shufps/peak-ignitor-hw/case/case.png

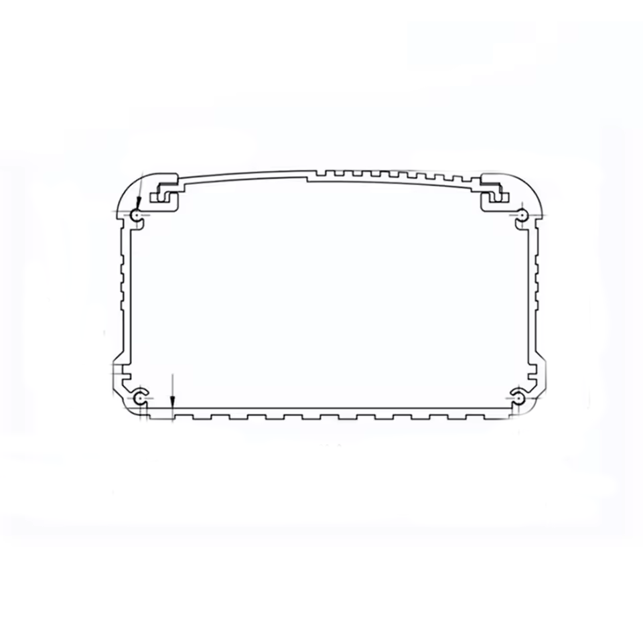
case/case.png
