shufps/peak-ignitor-hw/images/front.jpg

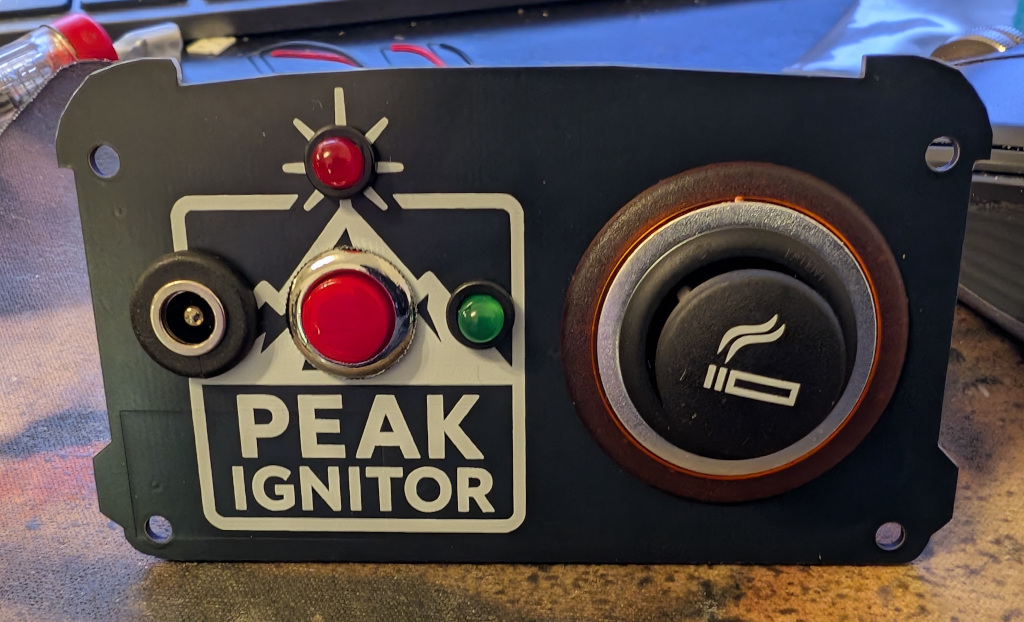
images/front.jpg
