shufps/peak-ignitor-hw/images/heatsink-front.jpg

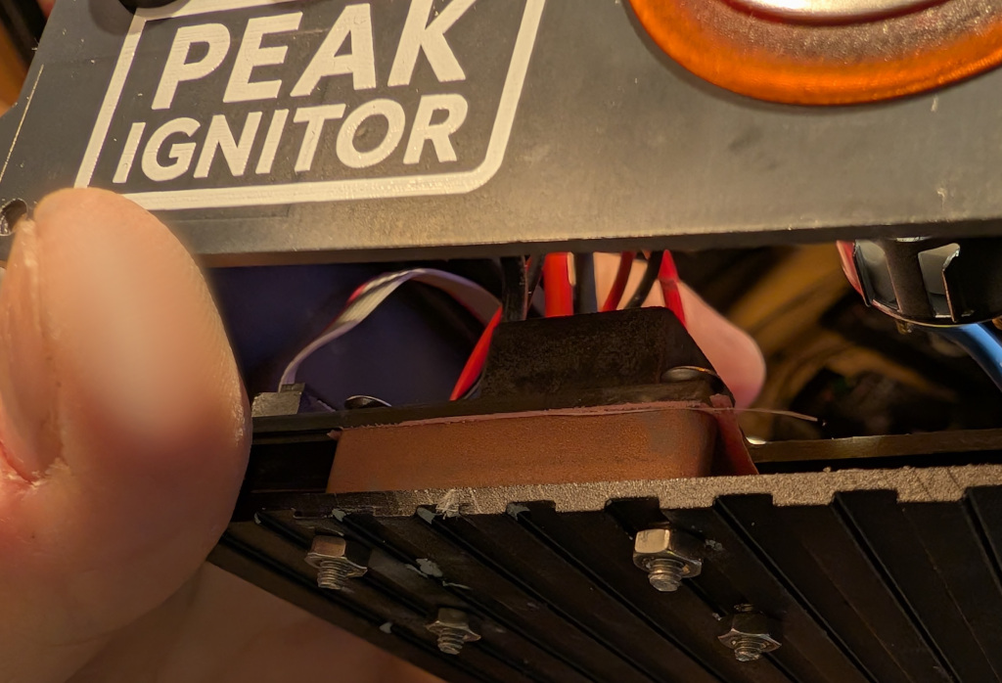
images/heatsink-front.jpg
