shufps/peak-ignitor-hw/images/heatsink-mounting.jpg

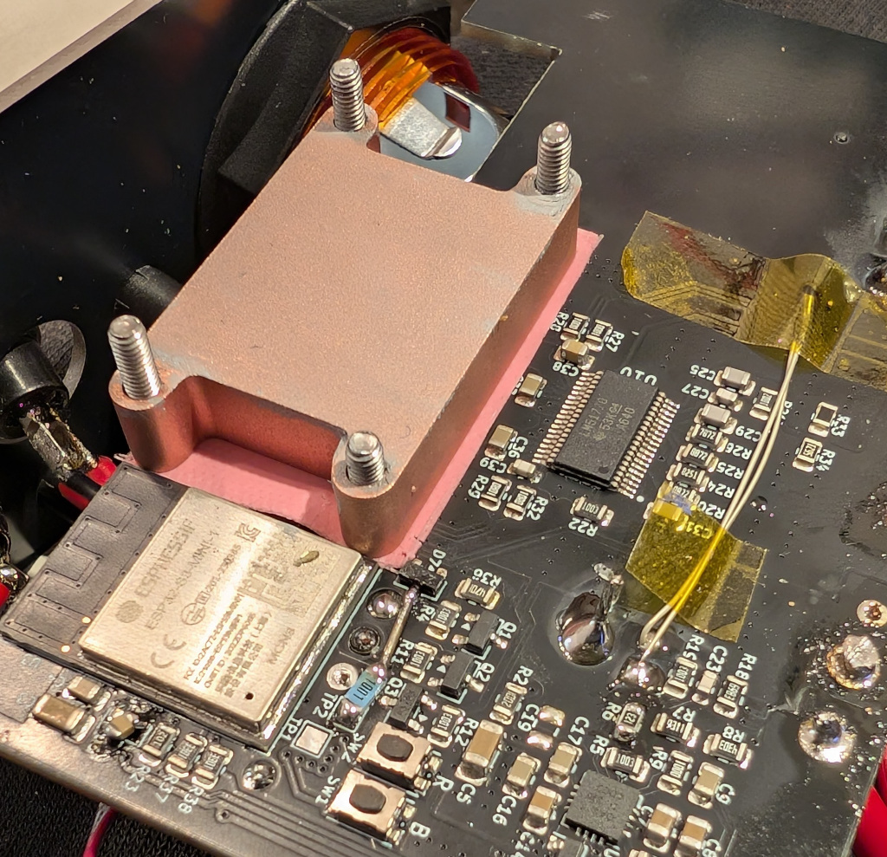
images/heatsink-mounting.jpg
