shufps/peak-ignitor-hw/kicad/3d/fuse_10a_render.png

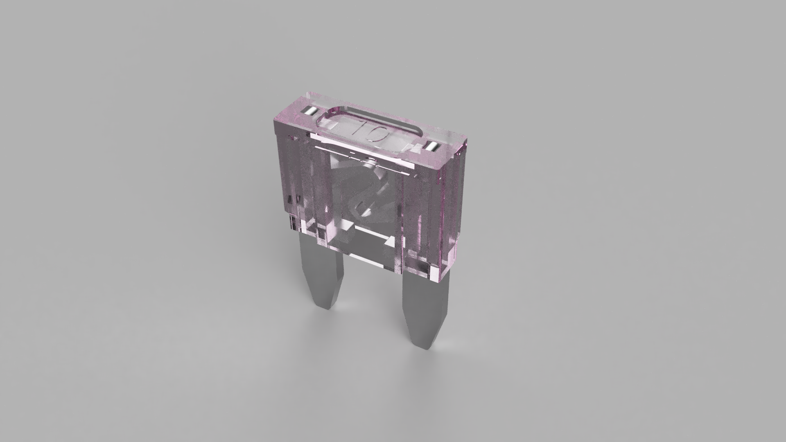
kicad/3d/fuse_10a_render.png
