shufps/peak-ignitor-hw/plots/120W-discharge_plot.png

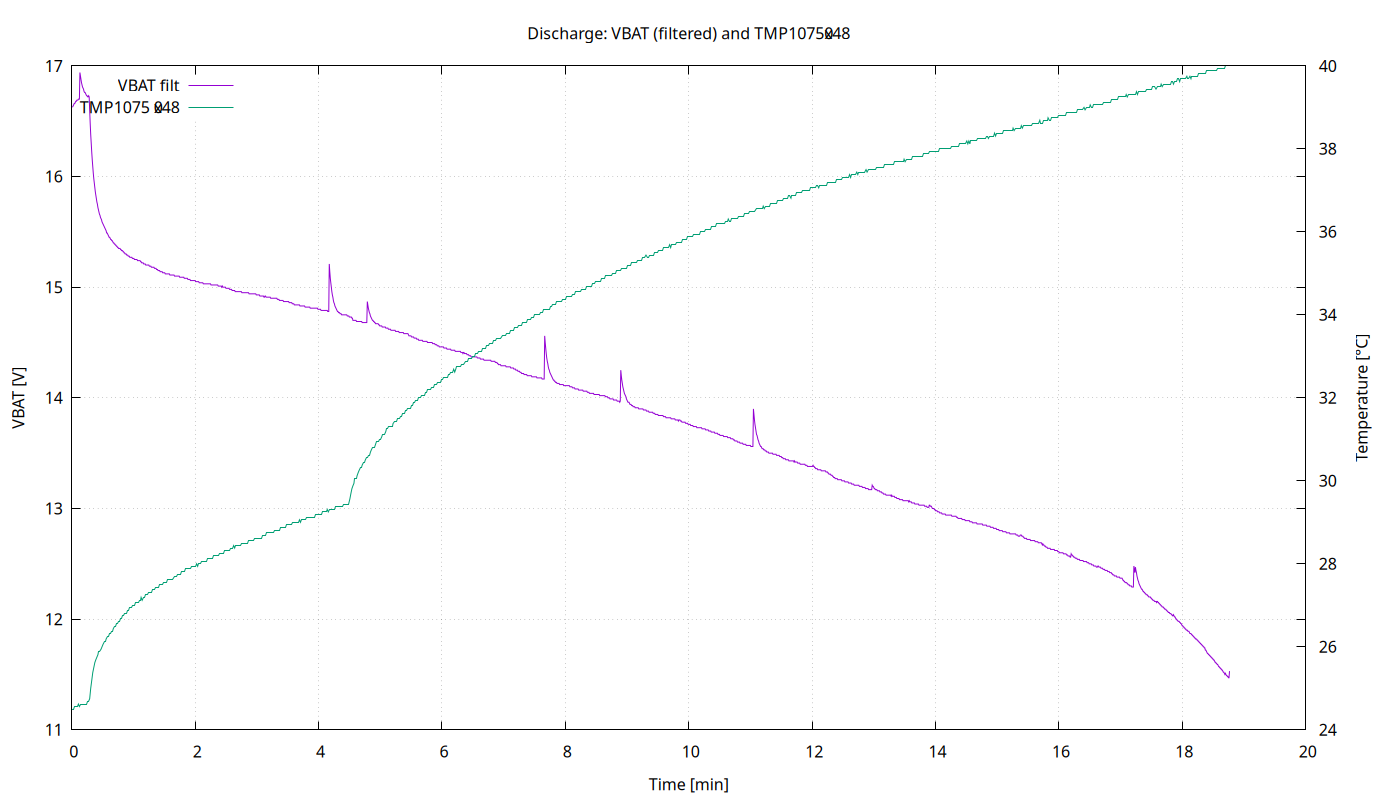
plots/120W-discharge_plot.png
