shufps/peak-ignitor-hw/plots/160W-discharge_plot.png

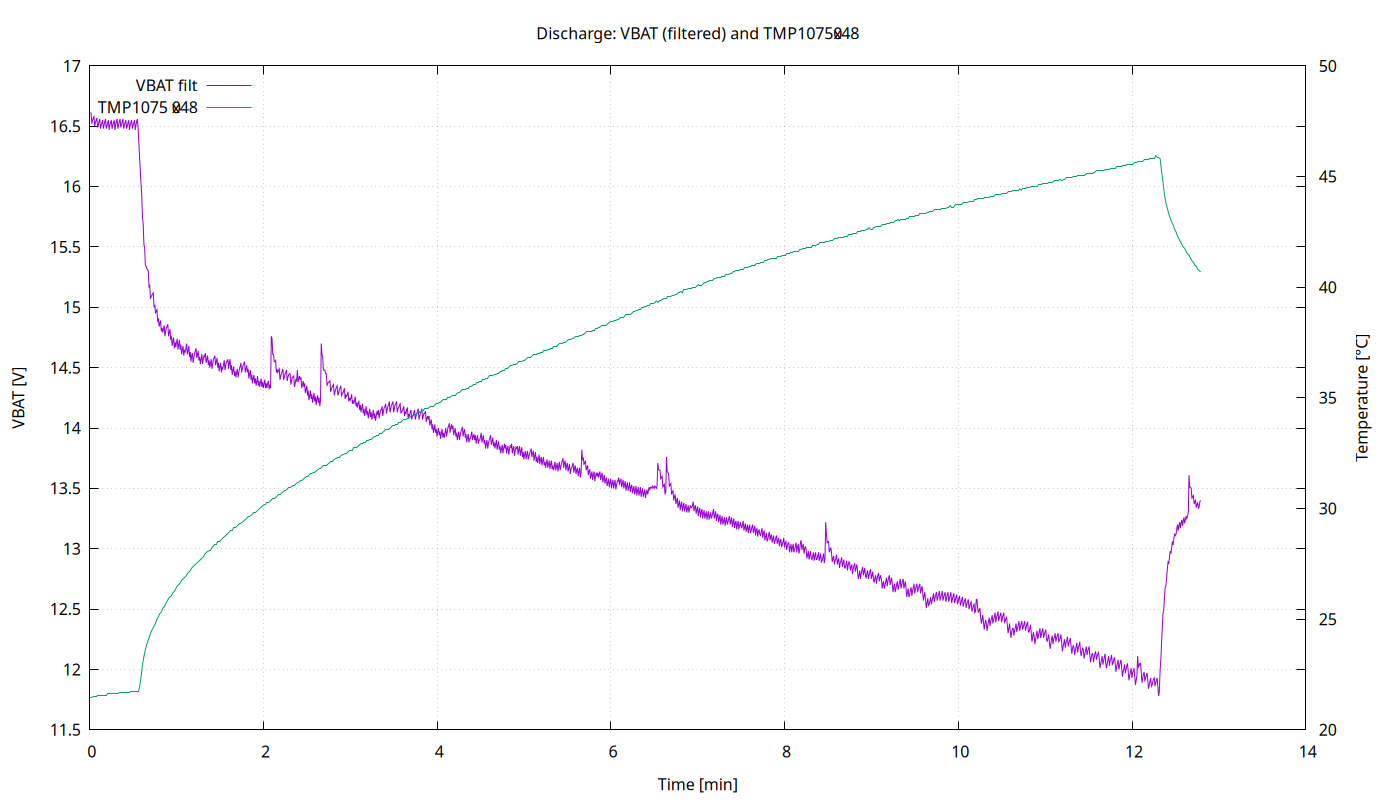
plots/160W-discharge_plot.png
