shufps/peak-ignitor-hw/plots/charge_plot.png

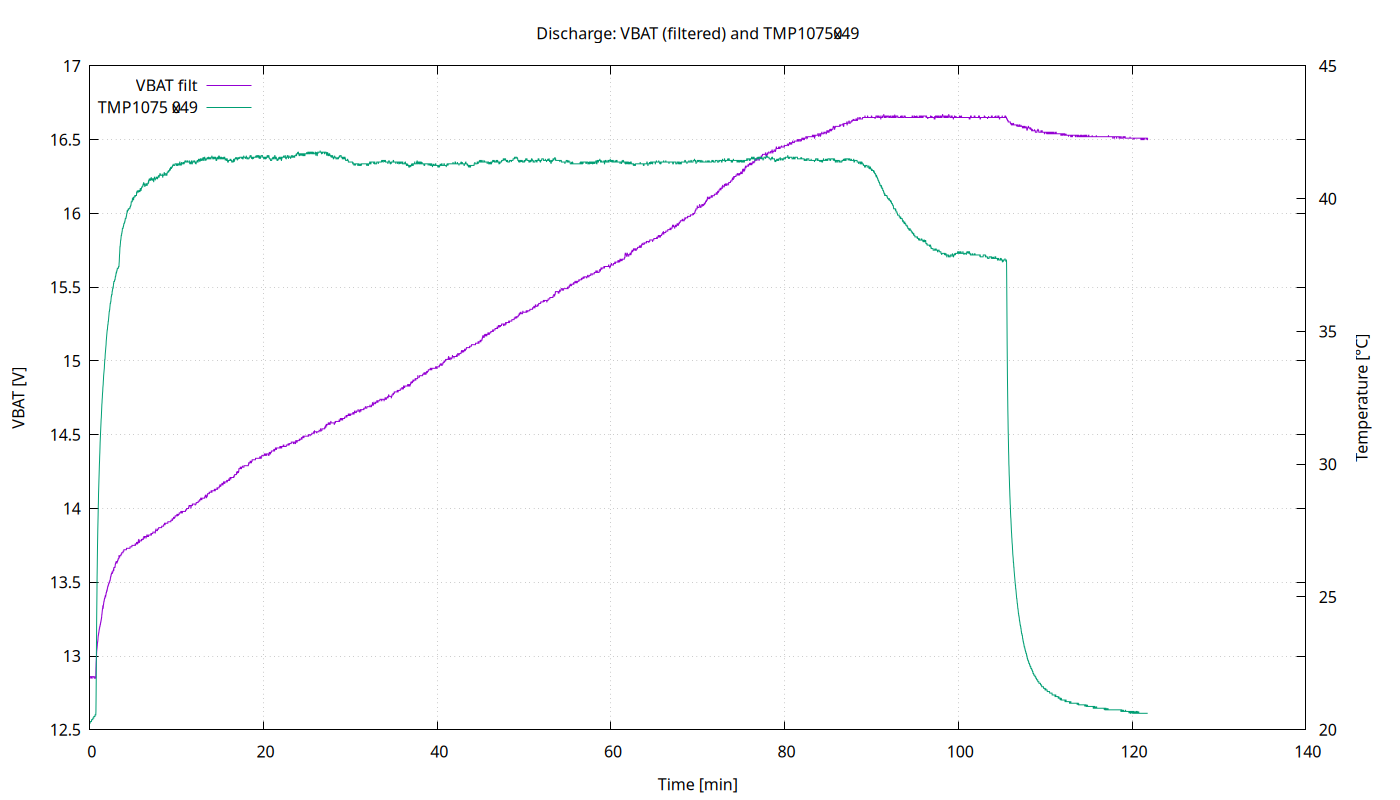
plots/charge_plot.png
