shufps/peak-ignitor-hw/bms-pcb/bom/71lHET93GKL._SL1200_.jpg

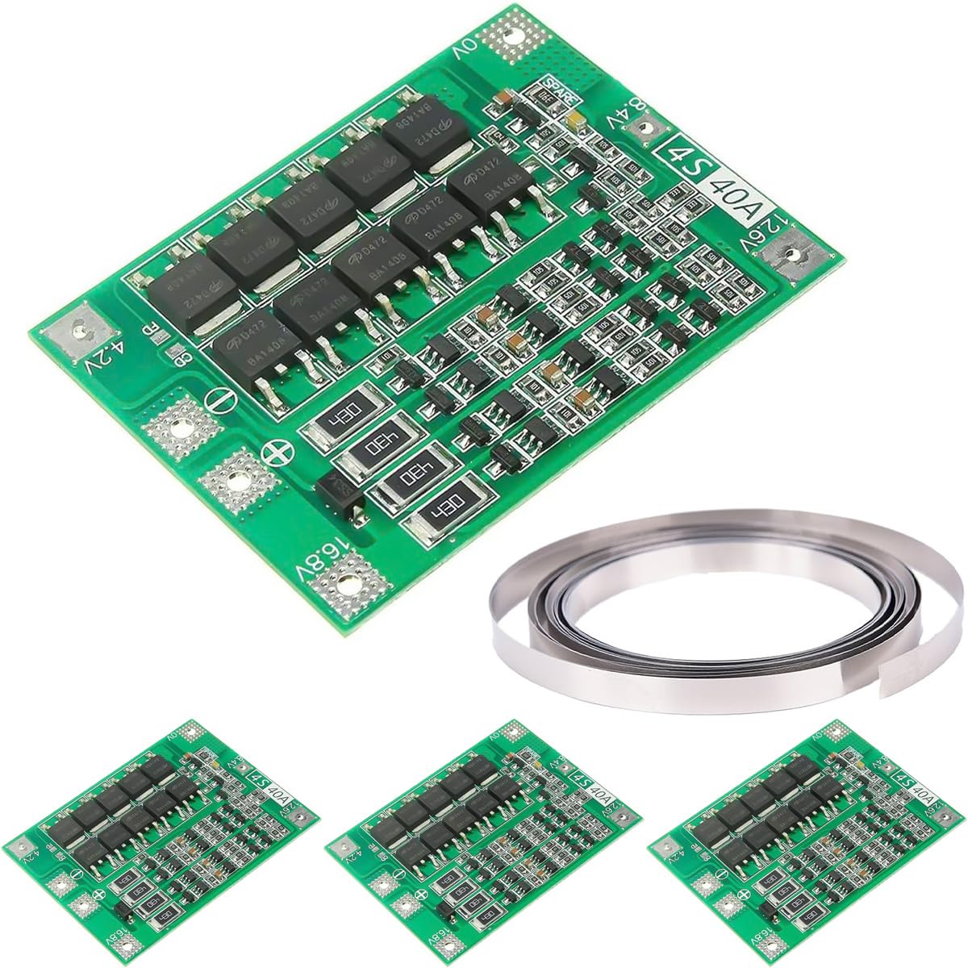
bms-pcb/bom/71lHET93GKL._SL1200_.jpg
