shufps/peak-ignitor-hw/kicad/3d/IND50X50FD.step

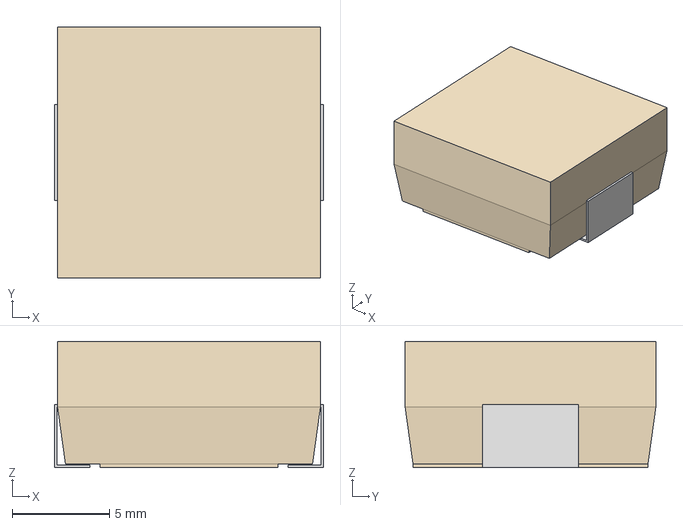
[picture p29: CAD file, 2025-12-20]
kicad/3d/IND50X50FD.step
13.8 x 12.9 x 6.50 mm
