shufps/peak-ignitor-hw/kicad/3d/led4_rtgn.stl

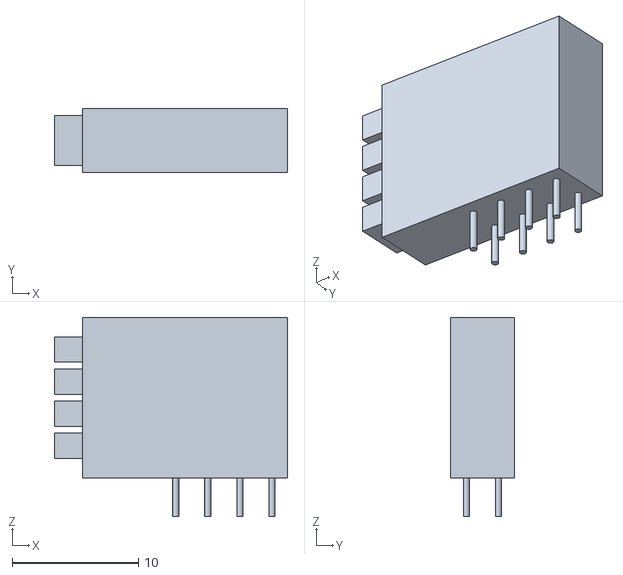
[picture p30: CAD file, 2025-12-20]
kicad/3d/led4_rtgn.stl
18.4 x 5.08 x 15.8
