shufps/peak-ignitor-hw/kicad/3d/barrel-jack.step

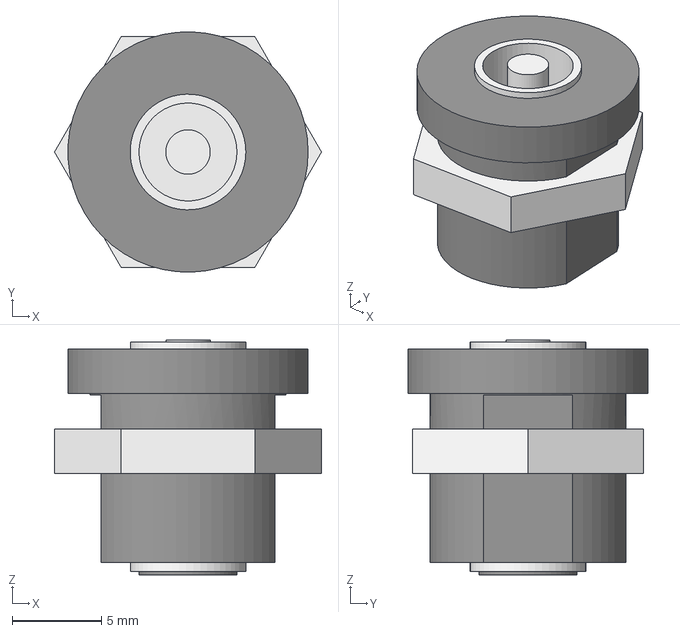
[picture p31: CAD file, 2025-12-20]
kicad/3d/barrel-jack.step
15.0 x 13.5 x 13.2 mm
