shufps/peak-ignitor-hw/kicad/3d/Fuse - mini 10A.step

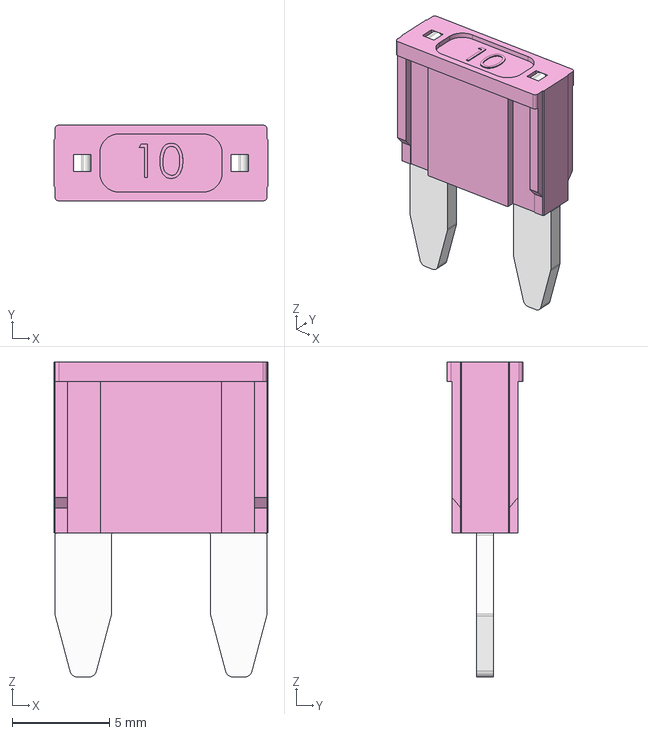
[picture p32: CAD file, 2025-12-20]
kicad/3d/Fuse - mini 10A.step
11.0 x 3.90 x 16.2 mm
