shufps/peak-ignitor-hw/kicad/3d/Littelfuse 0154.500DRT without value_black v2.step

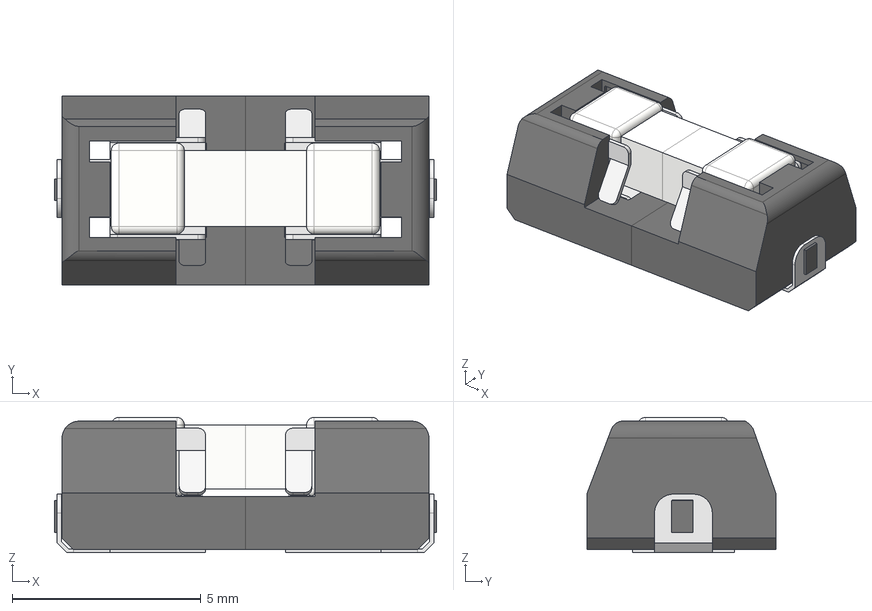
[picture p33: CAD file, 2025-12-20]
kicad/3d/Littelfuse 0154.500DRT without value_black v2.step
10.1 x 5.00 x 3.59 mm
Komponente1
Komponente2
Komponente3
Komponente4
