shufps/peak-ignitor-hw/kicad/3d/3mm_LED.stp

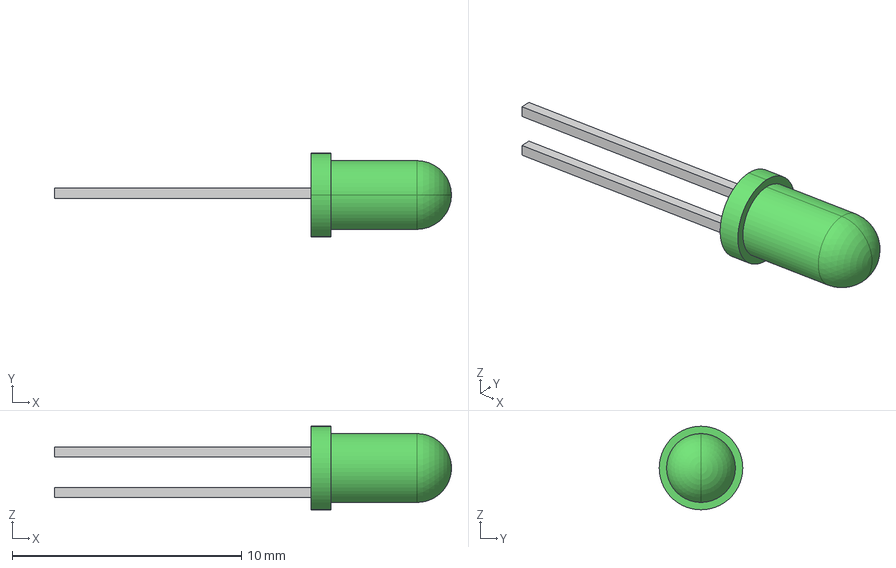
[picture p34: CAD file, 2025-12-20]
kicad/3d/3mm_LED.stp
17.3 x 3.64 x 3.64 mm
led_energy
led_pin.1.1.1
led_pin.2.1
