shufps/peak-ignitor-hw/kicad/3d/IDC_1.27mm_2x3.step

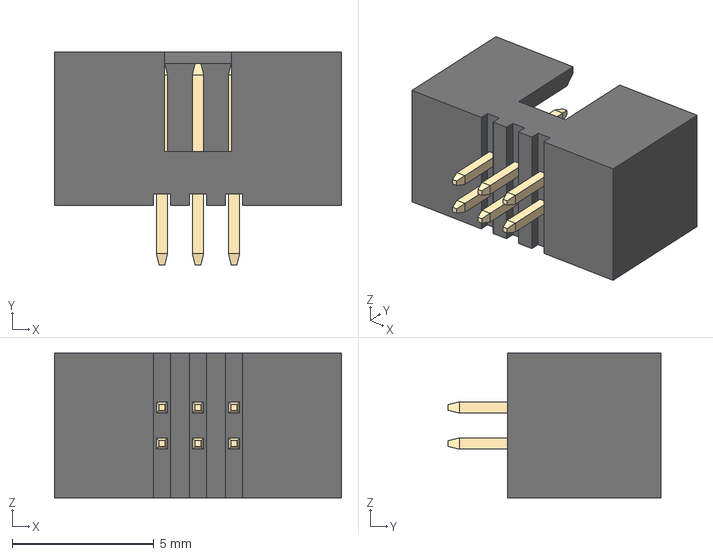
[picture p35: CAD file, 2025-12-20]
kicad/3d/IDC_1.27mm_2x3.step
10.1 x 7.50 x 5.10 mm
