shufps/peak-ignitor-hw/kicad/3d/SSF-LXH400HGW.step

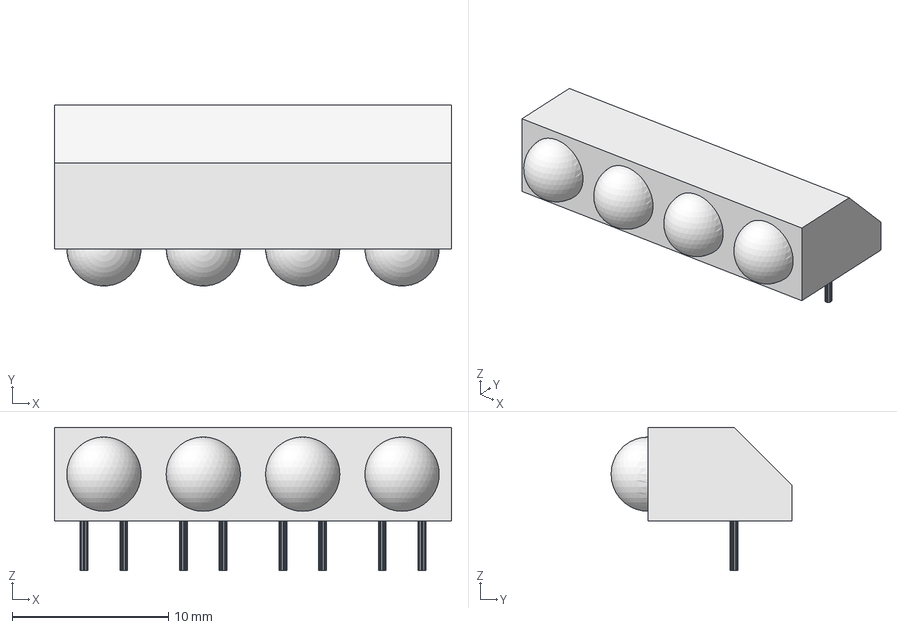
[picture p36: CAD file, 2025-12-20]
kicad/3d/SSF-LXH400HGW.step
25.4 x 11.6 x 9.18 mm
